xjtuecho/EDSPack/OwonBatteryCase/Pictures/20191029_072716.jpg

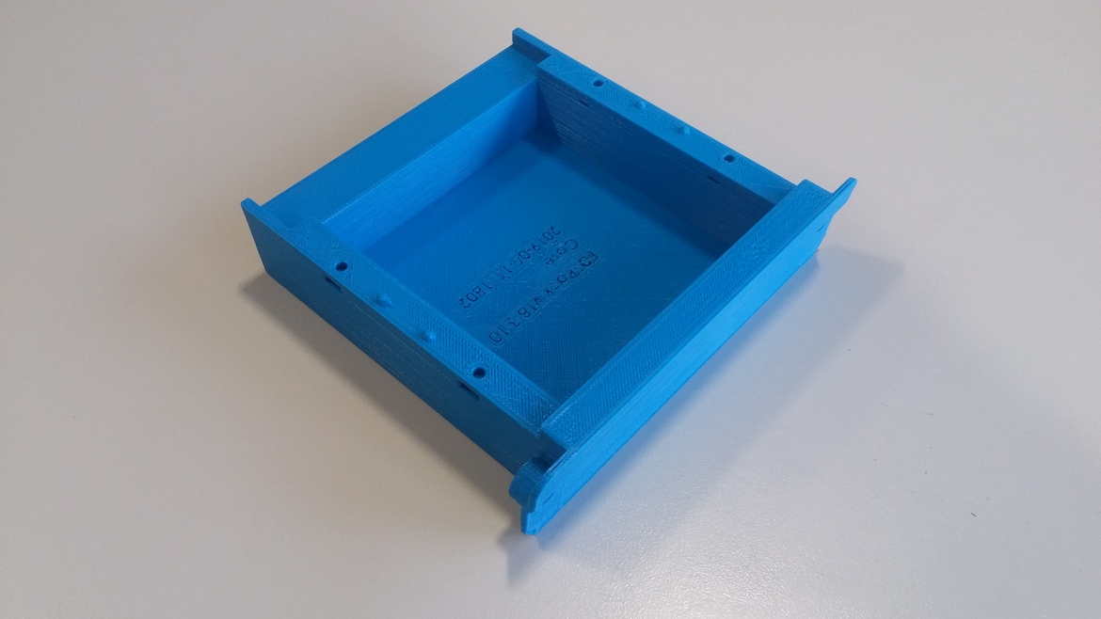
OwonBatteryCase/Pictures/20191029_072716.jpg
