xjtuecho/EDSPack/OwonBatteryCase/Pictures/20191029_073522.jpg

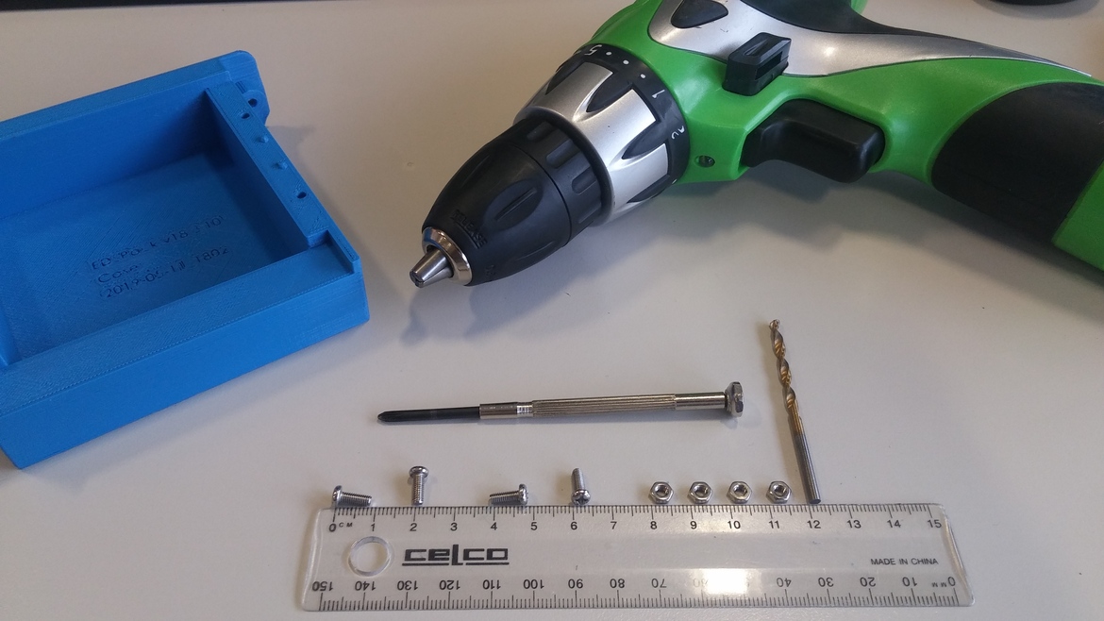
OwonBatteryCase/Pictures/20191029_073522.jpg
