xjtuecho/EDSPack/OwonBatteryCase/Pictures/20191029_073629.jpg

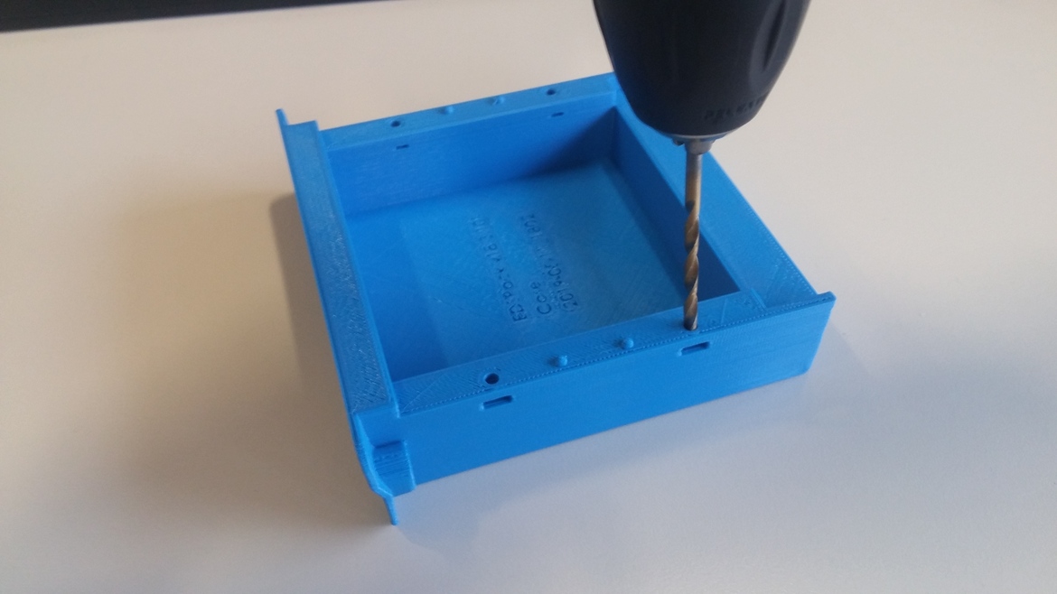
OwonBatteryCase/Pictures/20191029_073629.jpg
