xjtuecho/EDSPack/OwonBatteryCase/Pictures/20191029_074502.jpg

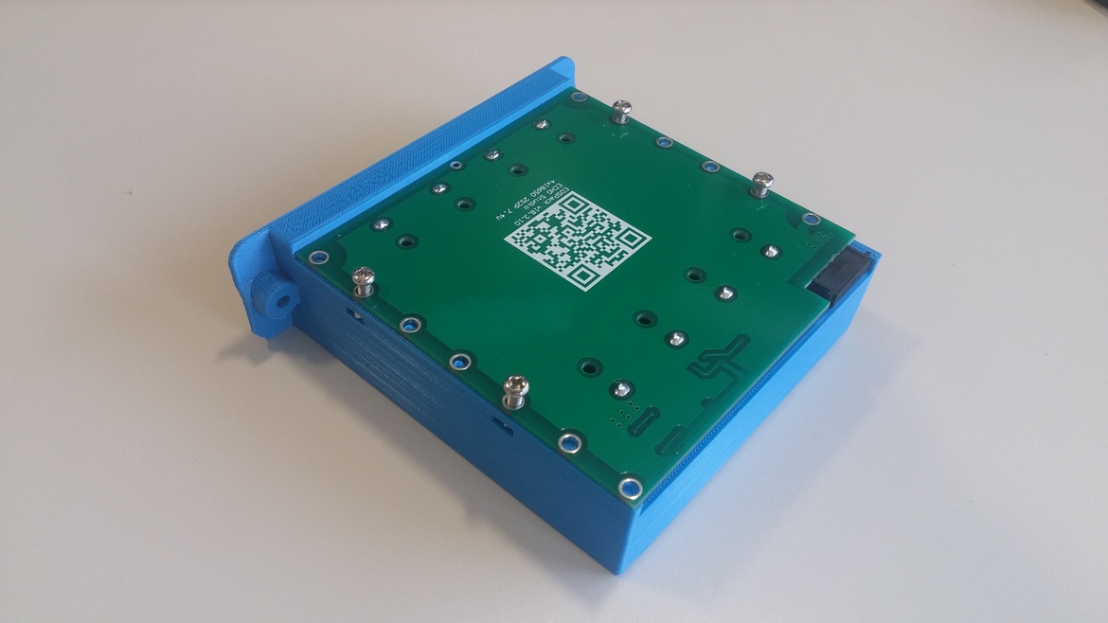
OwonBatteryCase/Pictures/20191029_074502.jpg
