xjtuecho/EDSPack/OwonBatteryCase/Pictures/20191029_074753.jpg

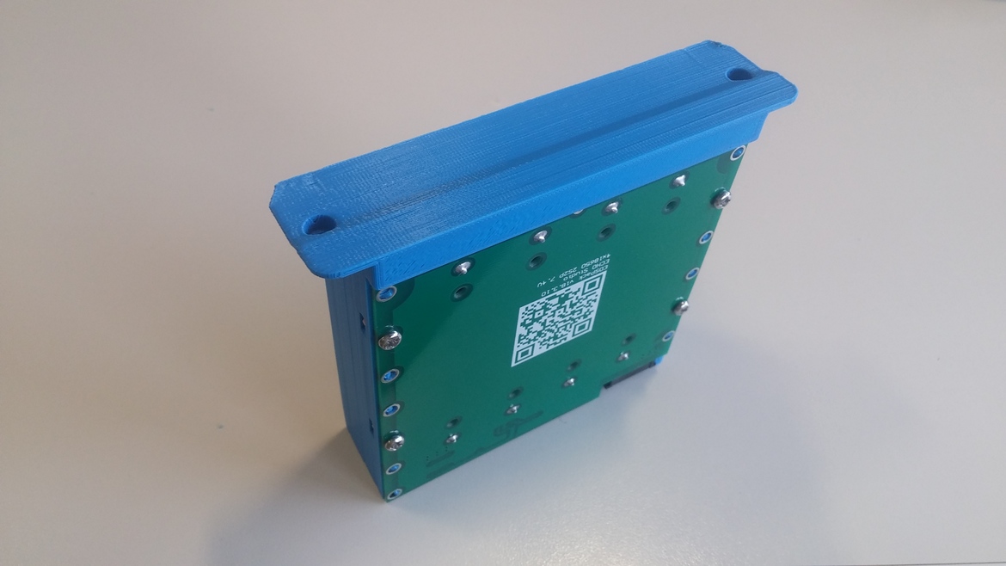
OwonBatteryCase/Pictures/20191029_074753.jpg
